Hob-dev/Orthus/Renders/OrthusWIP3.jpg

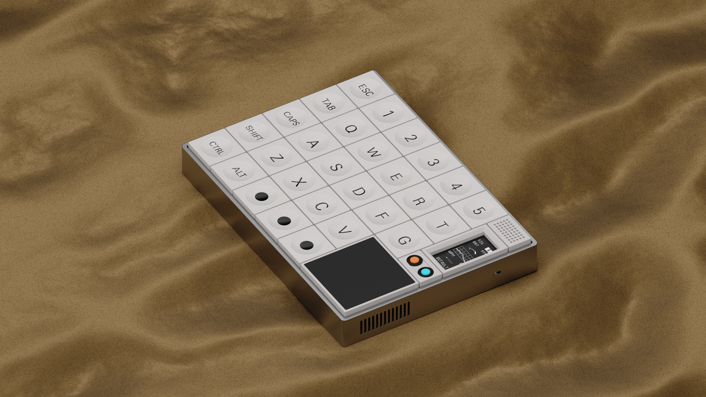
Renders/OrthusWIP3.jpg
