Hob-dev/Orthus/Renders/OrthusWIP6.png

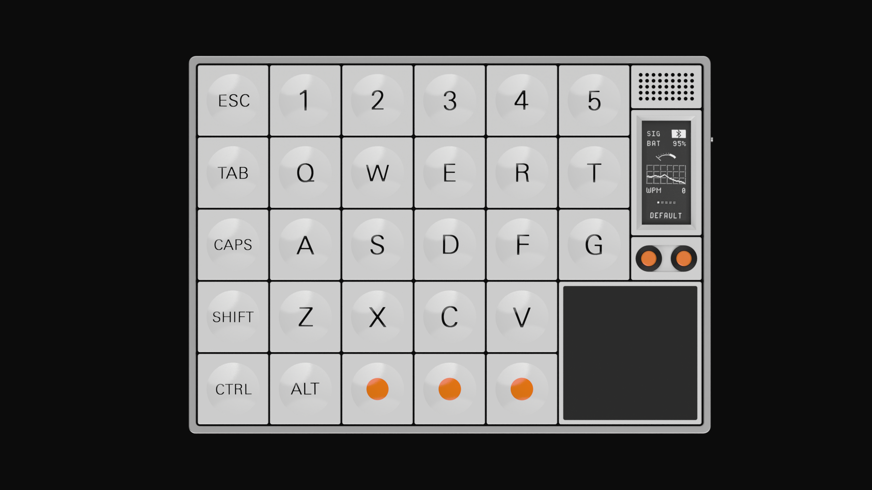
Renders/OrthusWIP6.png
