Hob-dev/Orthus/Renders/OrthusWIPALT1.jpg

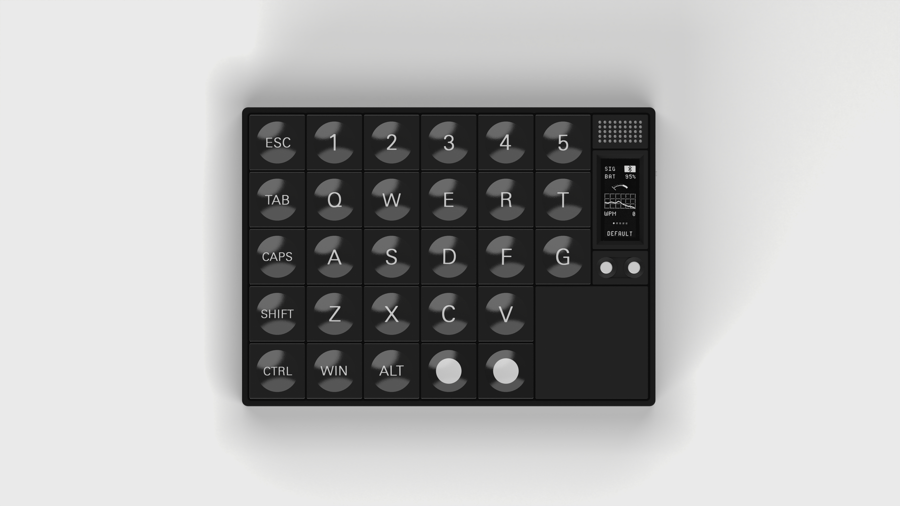
Renders/OrthusWIPALT1.jpg
