Hob-dev/Orthus/Renders/OrthusWIPALT.jpg

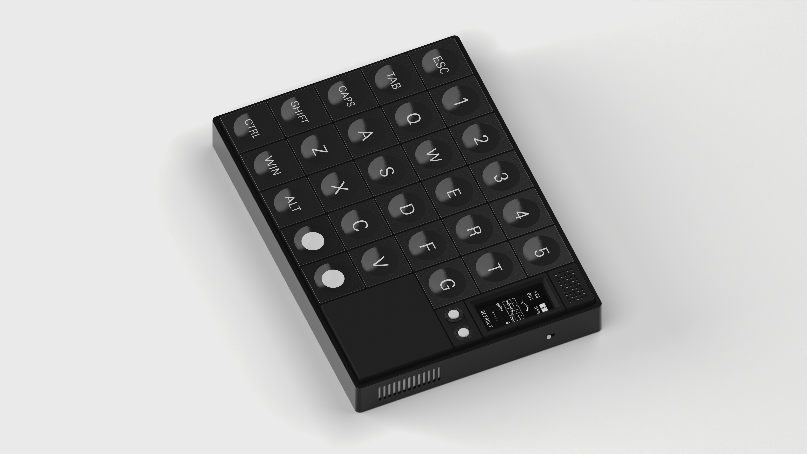
Renders/OrthusWIPALT.jpg
